Licastache/La-Rape-IA/Photos pour git/image00006.jpeg

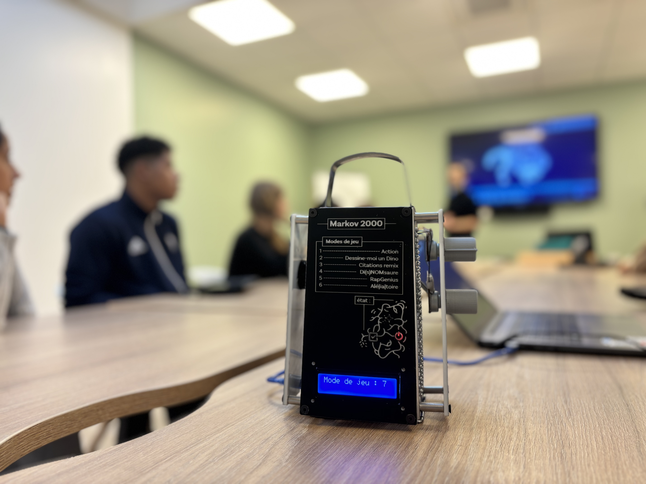
Photos pour git/image00006.jpeg
