Licastache/La-Rape-IA/Photos pour git/PXL_20241113_133846352.jpg

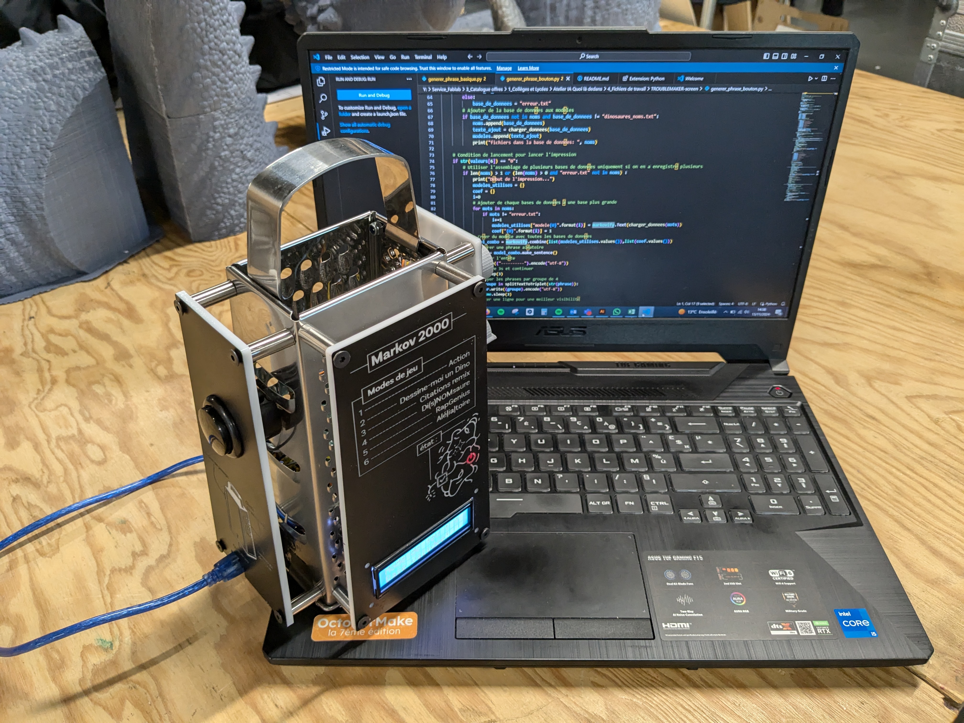
Photos pour git/PXL_20241113_133846352.jpg
